UniversalScientificTechnologies/ExpaLight/DOC/src/img/20160717_150406.jpg

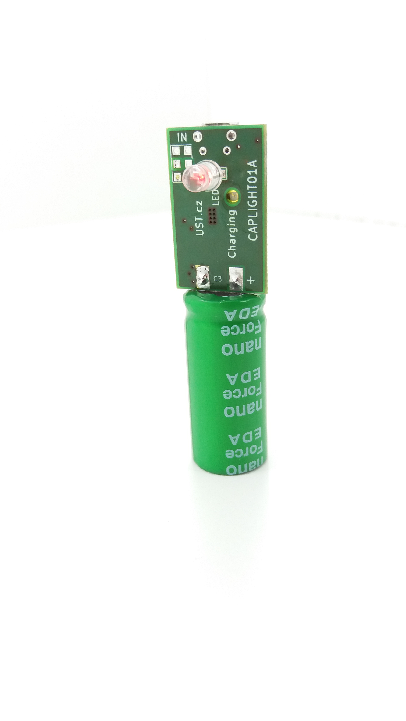
DOC/src/img/20160717_150406.jpg
