UniversalScientificTechnologies/ExpaLight/DOC/src/img/20160717_150523.jpg

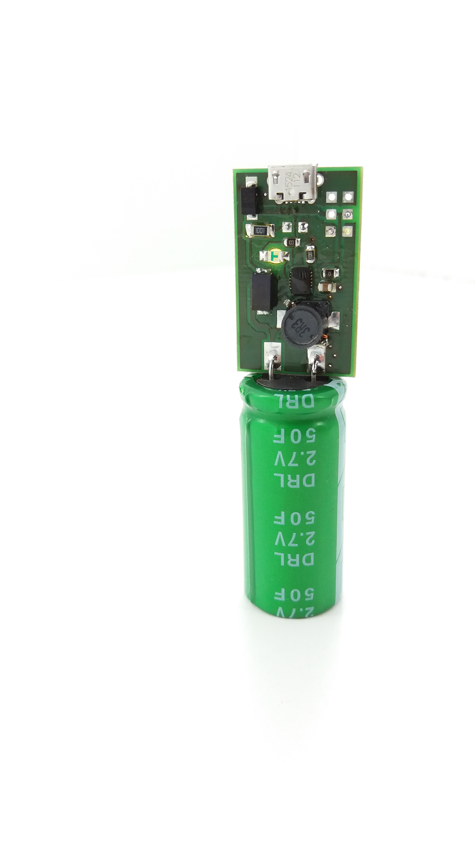
DOC/src/img/20160717_150523.jpg
