UniversalScientificTechnologies/ExpaLight/DOC/src/img/20161026_155425.jpg

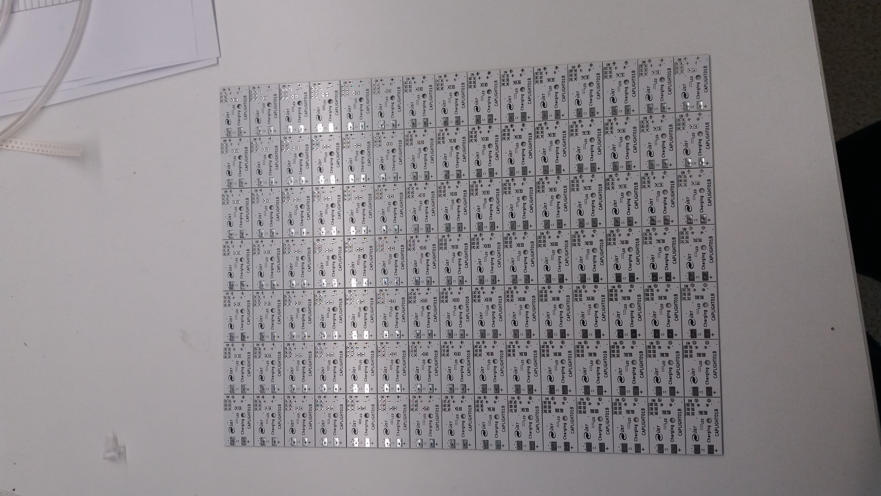
DOC/src/img/20161026_155425.jpg
