UniversalScientificTechnologies/ExpaLight/DOC/src/img/20161026_155428.jpg

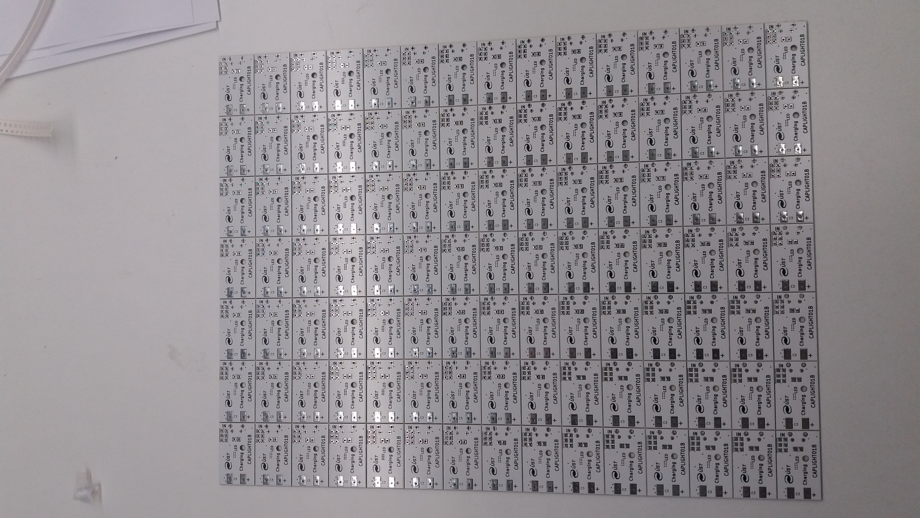
DOC/src/img/20161026_155428.jpg
