UniversalScientificTechnologies/ExpaLight/DOC/src/img/20161026_155517.jpg

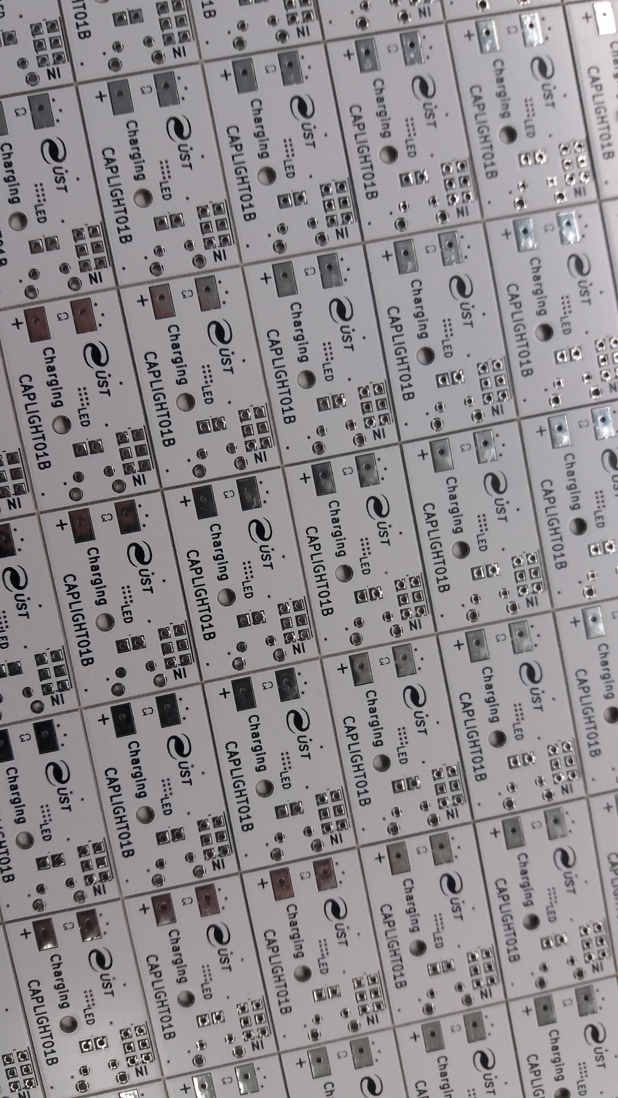
DOC/src/img/20161026_155517.jpg
