UniversalScientificTechnologies/ExpaLight/DOC/src/img/20161026_155519.jpg

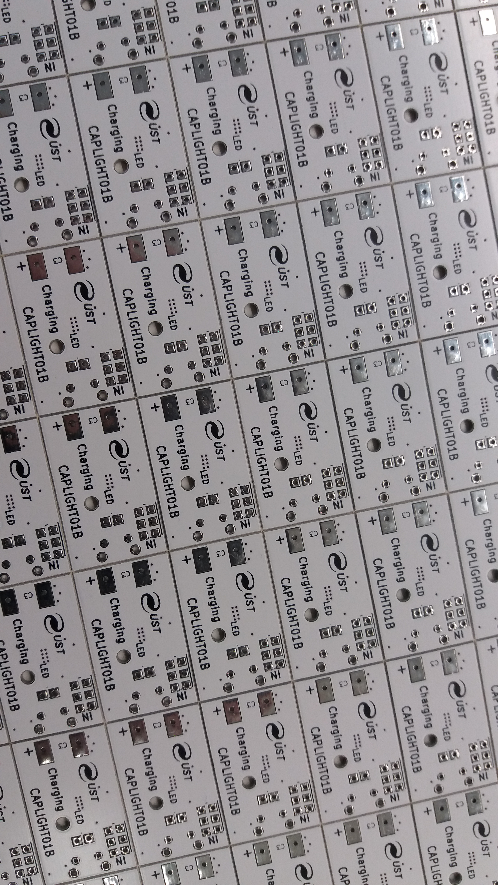
DOC/src/img/20161026_155519.jpg
