UniversalScientificTechnologies/ExpaLight/DOC/src/img/CAPLIGHT01B_PCB_Top.png

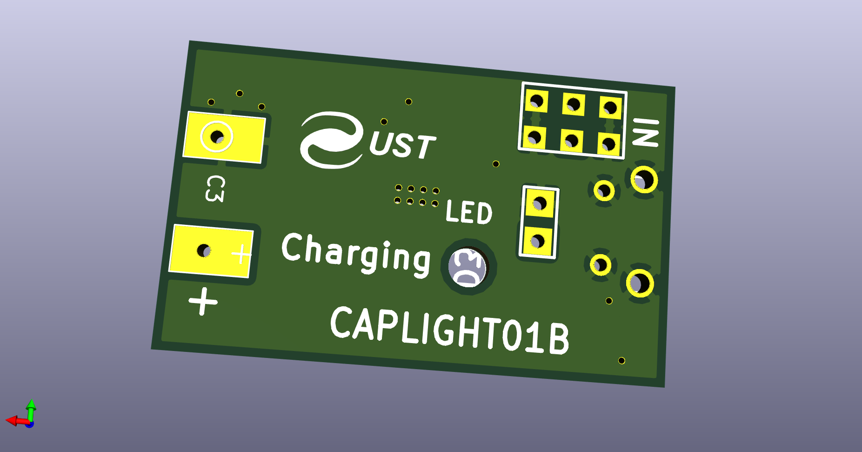
DOC/src/img/CAPLIGHT01B_PCB_Top.png
