UniversalScientificTechnologies/ExpaLight/DOC/src/img/IMG_1657-2.png

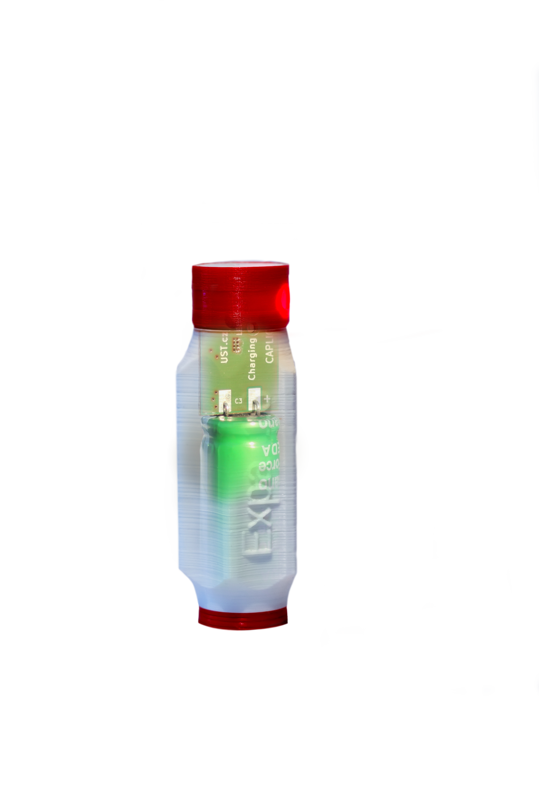
DOC/src/img/IMG_1657-2.png
