UniversalScientificTechnologies/ExpaLight/CAD/src/printplate/plast.scad

include <../CapaLamp.scad>

plast("Infinitas ∞", "ExpaLight");
